SolderedElectronics/4-channel-relay-board-hardware-design/OUTPUTS/V1.1.1/333022.jpg

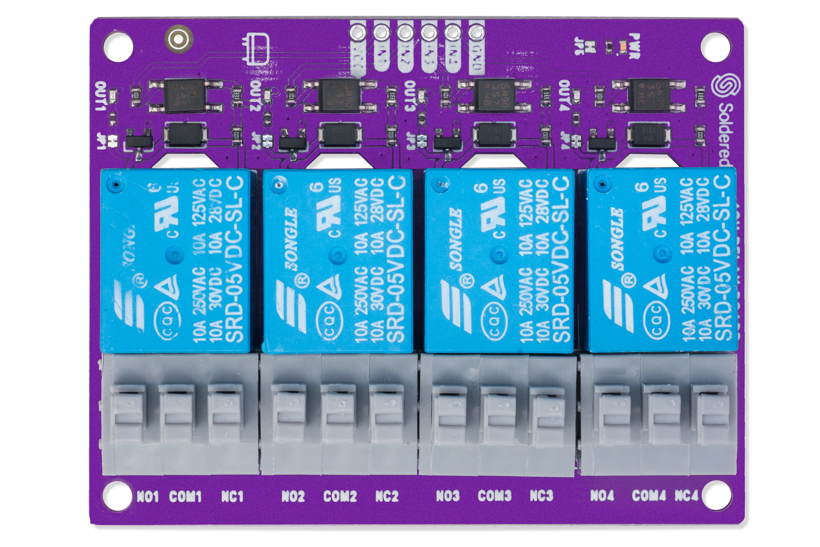
OUTPUTS/V1.1.1/333022.jpg
